74ls00/ESR_NM8032/0.png

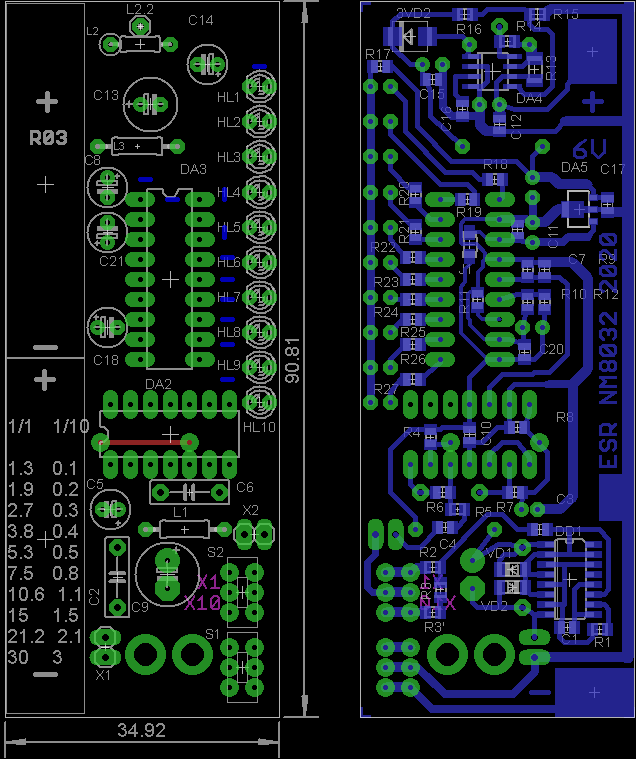
0.png
